MamudRostam/Mamud_Final_Year_Project/Documentation/1000193232.jpg

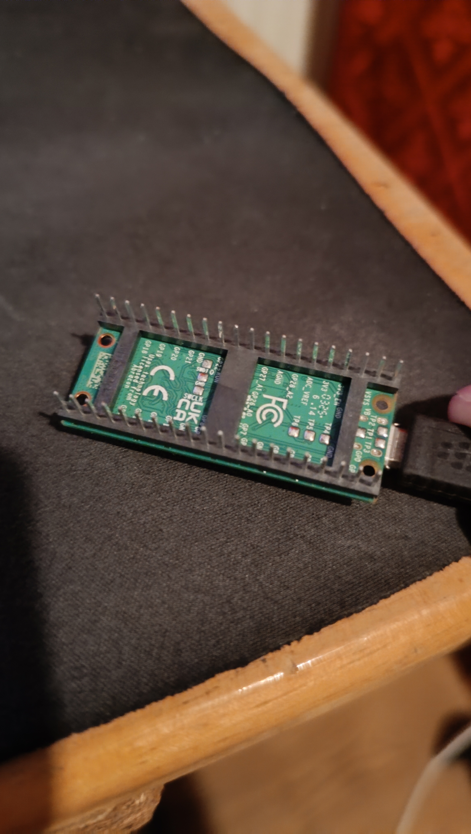
Documentation/1000193232.jpg
