MamudRostam/Mamud_Final_Year_Project/Documentation/1000193437.jpg

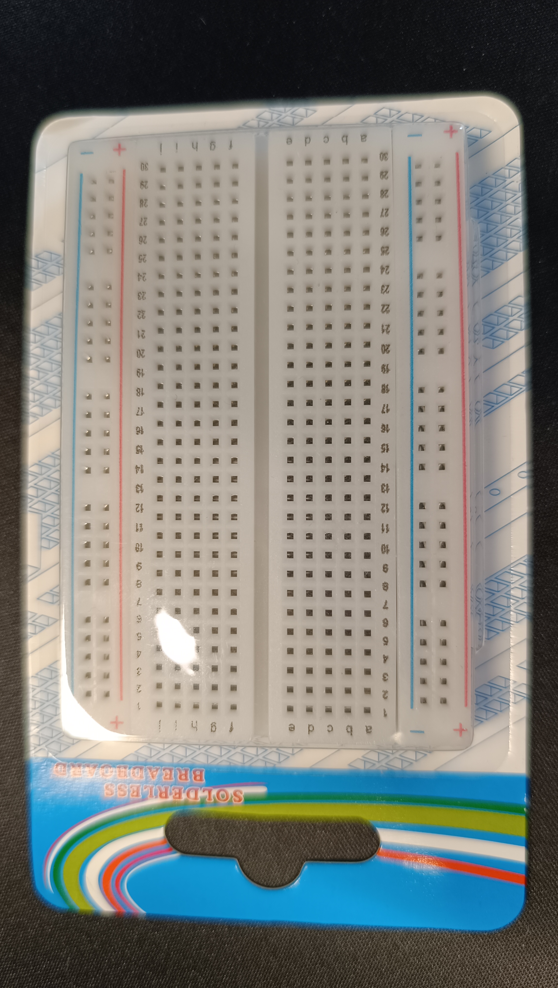
Documentation/1000193437.jpg
